Projects-and-Stuff/AttenuatorX/AttenuatorX/AttenuatorX.sch

## KiCad design AttenuatorX/AttenuatorX.sch (2011-11-27)

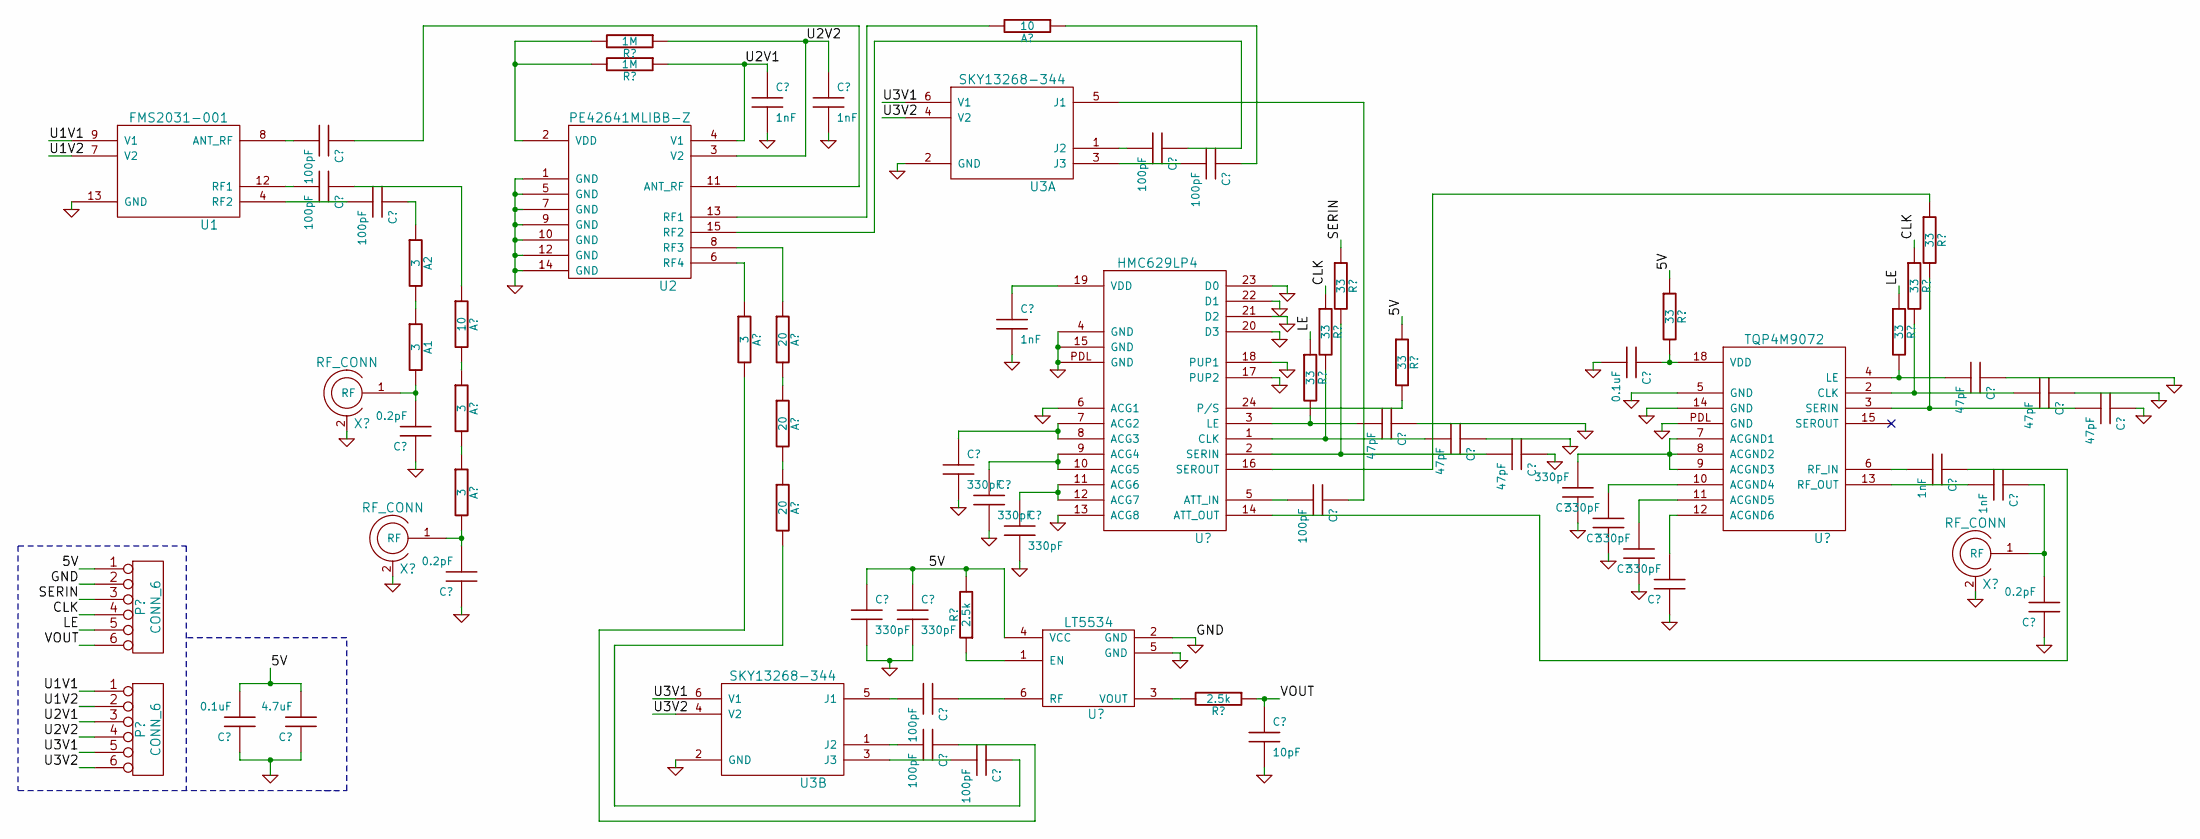
[picture p3: schematic AttenuatorX.sch]

Parts:
A1, A2: 3
U1: FMS2031-001
U2: PE42641MLIBB-Z
U3A, U3B: SKY13268-344

Connections:
GND: U1.13 (GND), U2.1 (GND), U2.5 (GND), U2.7 (GND), U2.9 (GND), U2.10 (GND), U2.12 (GND), U2.14 (GND), U3A.2 (GND), U3B.2 (GND)
unnamed: A1.1, A2.2
U1V1: U1.9 (V1)
U1V2: U1.7 (V2)
U2V1: U2.4 (V1)
U2V2: U2.3 (V2)
U3V1: U3A.6 (V1), U3B.6 (V1)
U3V2: U3A.4 (V2), U3B.4 (V2)
