Projects-and-Stuff/AttenuatorX/AttenuatorXLE/AttenuatorXLE.sch

## KiCad design AttenuatorXLE/AttenuatorXLE.sch (2011-11-30, an earlier design)

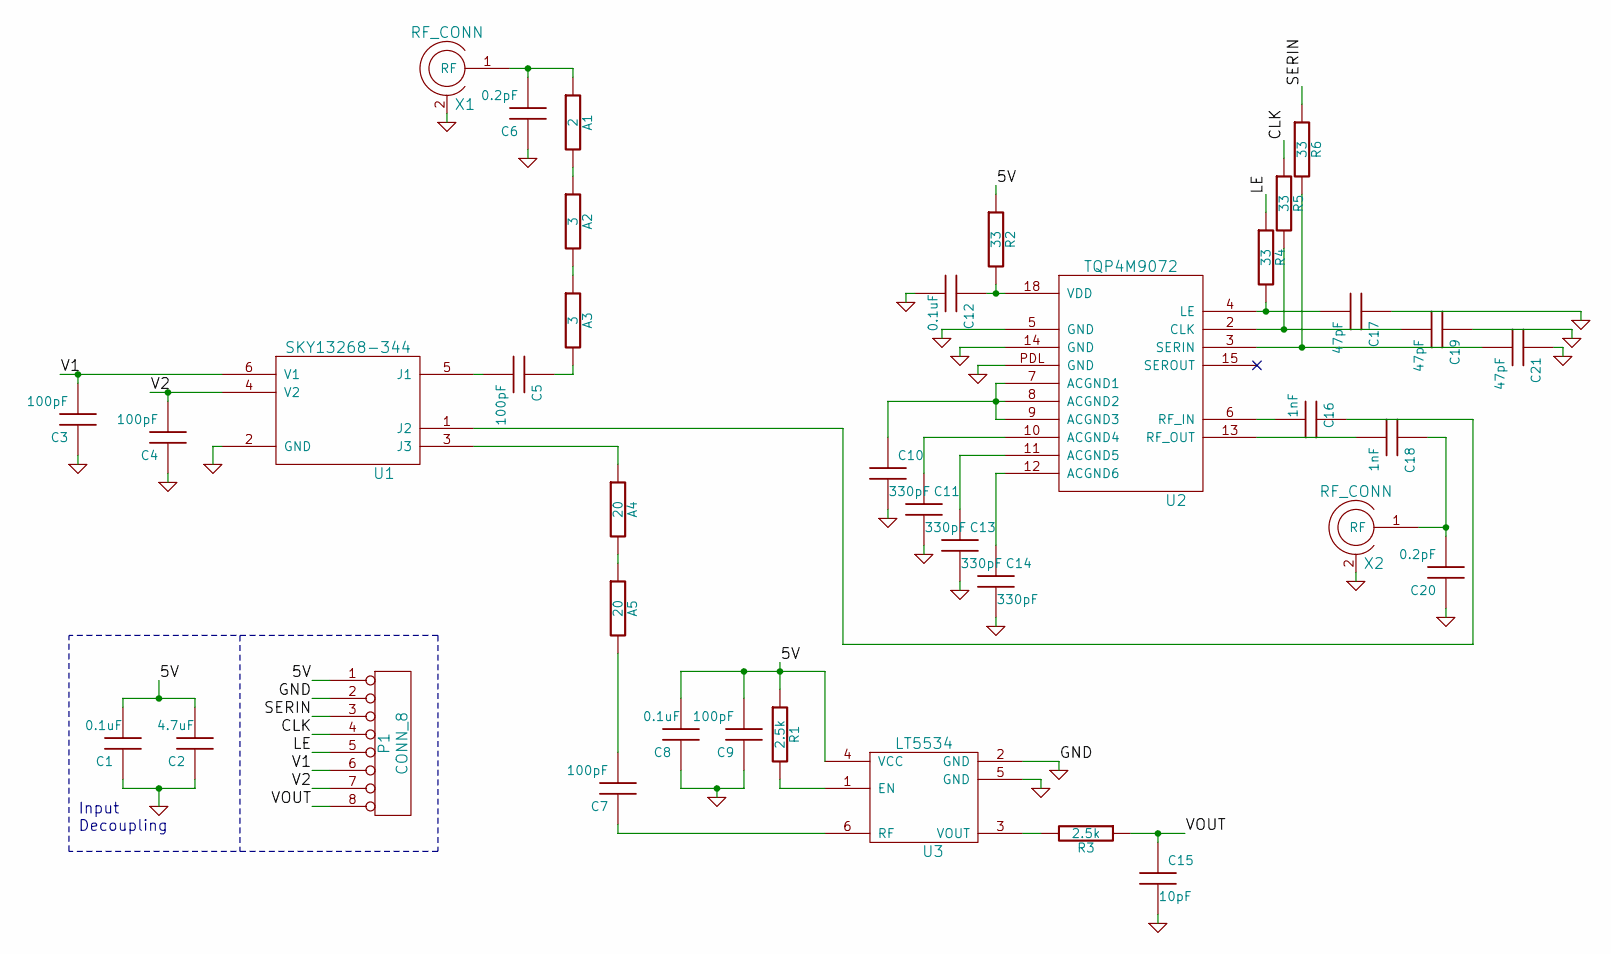
[picture p4: schematic AttenuatorXLE.sch]

Parts:
A1: 2
A2, A3: 3
A4, A5: 20
C1, C8, C12: 0.1uF
C2: 4.7uF
C3, C4, C5, C7, C9: 100pF
C6, C20: 0.2pF
C10, C11, C13, C14: 330pF
C15: 10pF
C16, C18: 1nF
C17, C19, C21: 47pF
P1: CONN_8
R1, R3: 2.5k
R2, R4, R5, R6: 33
U1: SKY13268-344
U2: TQP4M9072
U3: LT5534
X1, X2: RF_CONN

Connections:
5V: C1.2, C2.2, C8.2, C9.2, P1.1, R1.1, R2.1, U3.4 (VCC)
CLK: P1.4, R5.1
GND: C1.1, C2.1, C3.1, C4.1, C6.1, C8.1, C9.1, C10.2, C11.2, C12.2, C13.2, C14.2, C15.2, C17.1, C19.1, C20.1, C21.1, P1.2, U1.2 (GND), U2.5 (GND), U2.14 (GND), U2.PDL (GND), U3.2 (GND), U3.5 (GND), X1.2, X2.2
LE: P1.5, R4.1
unnamed: A1.1, C6.2, X1.1 (RF)
unnamed: A1.2, A2.1
unnamed: A2.2, A3.1
unnamed: A3.2, C5.1
unnamed: A4.1, U1.3 (J3)
unnamed: A4.2, A5.1
unnamed: A5.2, C7.2
unnamed: C5.2, U1.5 (J1)
unnamed: C7.1, U3.6 (RF)
unnamed: C10.1, U2.7 (ACGND1), U2.8 (ACGND2), U2.9 (ACGND3)
unnamed: C11.1, U2.10 (ACGND4)
unnamed: C12.1, R2.2, U2.18 (VDD)
unnamed: C13.1, U2.11 (ACGND5)
unnamed: C14.1, U2.12 (ACGND6)
unnamed: C16.1, U1.1 (J2)
unnamed: C16.2, U2.6 (RF_IN)
unnamed: C17.2, R4.2, U2.4 (LE)
unnamed: C18.1, C20.2, X2.1 (RF)
unnamed: C18.2, U2.13 (RF_OUT)
unnamed: C19.2, R5.2, U2.2 (CLK)
unnamed: C21.2, R6.2, U2.3 (SERIN)
unnamed: R1.2, U3.1 (EN)
unnamed: R3.2, U3.3 (VOUT)
SERIN: P1.3, R6.1
V1: C3.2, P1.6, U1.6 (V1)
V2: C4.2, P1.7, U1.4 (V2)
VOUT: C15.1, P1.8, R3.1

Notes on the sheet:
Input Decoupling
